j3qq4hch/PIXEL/Simulations/LED Driver.asc

C1: cap; 1.6p
C2: cap; 4p
C3: cap; 5pF
L1: ind; 0.1n
L2: ind; 0.1n
R1: res; 50K
R2: res; 6K
V1: voltage; PULSE(0 5 0 5n 5n 10u 20u)
Named nets: 0
.tran 30u
