j3qq4hch/PIXEL/Simulations/stepdown.asc

C1: cap; 10µ
C5: cap; 10µ
C7: cap; 10µ
C8: cap; 10µ
D3: schottky; MBRS340
I2: current; PULSE(10m 500m 0 10n 10n 500u 1000u)
L2: ind; 47µ
M1: nmos; IRLML0040
M2: pmos; FDC5614P
R1: res; 300R
R2: res; 1R
V3: voltage; 36
V4: voltage; PULSE(0 5 0 10n 10n 1.2u 10u); Rser=300R Cpar=10p
Named nets: 0
.tran 5m
