j3qq4hch/PIXEL/moustache_board/moustache/app/led_matrix/5x7_font.c

#include "5x7_font.h"


const u8 font_data[] = {0x00,                                   //first unusable char
                        0x00,                                   //space char    1
                        0x1D,                                   //!             2           
                        0x10,0x10,                              //"             3
                        0x00,                                   //#             5
                        0x00,                                   //$             6
                        0x18,0x19,0x02,0x04,0x08,0x13,03,       //%             7
                        0x00,                                   //&             14
                        0x18,                                   //'             15
                        0x0E,0x11,                              //(             16
                        0x11,0x0E,                              //)             18
                        0x14,0x08,0x14,                         //*             20
                        0x04,0x0E,0x04,                         //+             23
                        0x01,0x02,                              //,             26
                        0x04,0x04,0x04,                         //-             28
                        0x01,                                   //.             31
                        0x01,0x02,0x04,0x08,0x10,               // /            32
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
                        184,    //_
                        187,    //'
                        188,    //}
                        191,    //|
                        192,    //{
                        195,    //~
                        199
};      

const u8 font_len = ARRAY_SIZE(font_pos);
