j3qq4hch/PIXEL/moustache_board/moustache/app/inc/stm32_it.h

/**
  ******************************************************************************
  * @file    stm32_it.h 
  * @author  MCD Application Team
  * @version V1.0.0
  * @date    31-January-2014
  * @brief   This file contains the headers of the interrupt handlers.
  ******************************************************************************
  * @attention
  *
  * <h2><center>&copy; COPYRIGHT 2014 STMicroelectronics</center></h2>
  *
  * Licensed under MCD-ST Liberty SW License Agreement V2, (the "License");
  * You may not use this file except in compliance with the License.
  * You may obtain a copy of the License at:
  *
  *        http://www.st.com/software_license_agreement_liberty_v2
  *
  * Unless required by applicable law or agreed to in writing, software 
  * distributed under the License is distributed on an "AS IS" BASIS, 
  * WITHOUT WARRANTIES OR CONDITIONS OF ANY KIND, either express or implied.
  * See the License for the specific language governing permissions and
  * limitations under the License.
  *
  ******************************************************************************
  */ 

/* Define to prevent recursive inclusion -------------------------------------*/
#ifndef __STM32_IT_H
#define __STM32_IT_H

#ifdef __cplusplus
 extern "C" {
#endif 



void NMI_Handler(void);
void HardFault_Handler(void);
void SVC_Handler(void);
void PendSV_Handler(void);
void SysTick_Handler(void);
void TIM2_IRQHandler(void);
void EXTI4_15_IRQHandler(void);
void ADC1_IRQHandler(void);
void DMA1_Channel1_IRQHandler(void);
void TIM3_IRQHandler(void);

void USART1_IRQHandler(void);
#ifdef __cplusplus
}
#endif

#endif /* __STM32Fxxx_IT_H */

/************************ (C) COPYRIGHT STMicroelectronics *****END OF FILE****/
