j3qq4hch/PIXEL/moustache_board/moustache/app/inc/types.h

#ifndef __TYPES
#define __TYPES

#include "stm32f0xx.h"
#include "bitdef.h"

#ifndef NULL
#define NULL    0
#endif

typedef uint32_t  u32;
typedef uint16_t u16;
typedef uint8_t  u8;

typedef int32_t  s32;
typedef int16_t s16;
typedef int8_t  s8;

#endif
