j3qq4hch/PIXEL/moustache_board/moustache/app/led_matrix/5x7_font.h

#ifndef __5X7_FONT
#define __5X7_FONT

#include "types.h"

#define ARRAY_SIZE(arr)         (sizeof(arr) / sizeof(arr[0]))

extern const u8 font_pos[];
extern const u8 font_data[];
extern const u8 font_len;

#endif
