j3qq4hch/PIXEL/moustache_board/moustache/app/tmp/fft.h

/************************************************************************
	fft.h

   // FFT Audio Analysis
    Copyright (C) 2011 Simon Inns

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
	Email: simon.inns@gmail.com

************************************************************************/

#ifndef _FFT_H
#define _FFT_H

#include "types.h"

// Definitions
#define N_WAVE      1024    // full length of Sinewave[]
#define LOG2_N_WAVE 10      // log2(N_WAVE)


//void fix_fft(int fr[], int fi[], int m);
void fix_fft(s16 fr[], s16 fi[], u16 m);
unsigned int root(unsigned int x);
#endif 
