j3qq4hch/PIXEL/LE table/LE_table_stm32f103/util/types.h

#ifndef __TYPES
#define __TYPES
#include "stm32f10x.h"

#define ARRAY_SIZE(arr) (sizeof(arr) / sizeof(arr[0]))

#define BIT0	1
#define BIT1	2
#define BIT2	4
#define BIT3	8
#define BIT4	16
#define BIT5	32
#define BIT6	64
#define BIT7	128

#endif
